Collab-Barco-Solar/telemetria-DSB-2020/code/modules/cells/adc/adc_test_pot/adc_test_pot.ino

#include <Wire.h>

#define   ADC_12BIT_MAX   4096
#define   BAUD 2000000
#define   pin 4
#define   p5 17.5938359490609
#define   p4  1.21697808640912 
#define   p3  -0.000168313273959029
#define   p2  7.69758075646963e-08
#define   p1  -1.21956845031952e-11 

double valuefitted;
double potvoltage;
double stoptime;
double start;
double value = 0;
float DT5_RATIO = 1.552971576f; // VOLTAGE DIVIDER FOR POTENTIOMETER
void setup() {
  Serial.begin(BAUD);
  pinMode(pin, INPUT);
  /* aguarda a serial estar disponível */
  while (!Serial);
  
}

void loop() {
  
  value = analogRead(pin);
  //.print("Valor lido Logico: ");
  //Serial.print(value);
  //Serial.print(" : ");
  start = micros();
  valuefitted = (value*value*value*value*p1)+(value*value*value*p2)+(value*value*p3) + (value*p4) + p5;
  potvoltage = (valuefitted * 3.3)/4095;
  stoptime = micros();
  //Serial.print("Valor ajustado Logico: ");
  //Serial.print(valuefitted);
  //Serial.print(" ; ");
  //Serial.print("Tensao de leitura ajustada: ");
  //Serial.print(potvoltage);
  //Serial.print(" ; ");
  Serial.print("Posicao POT: ");
  Serial.print(potvoltage * DT5_RATIO * 2,1);
  Serial.print(" ; ");
  
  Serial.print(stoptime-start);
  Serial.println(" ; ");
  delay(500);
}
